albeerto-dev/Brewing_PLC/Images/Ricette_implementate.png

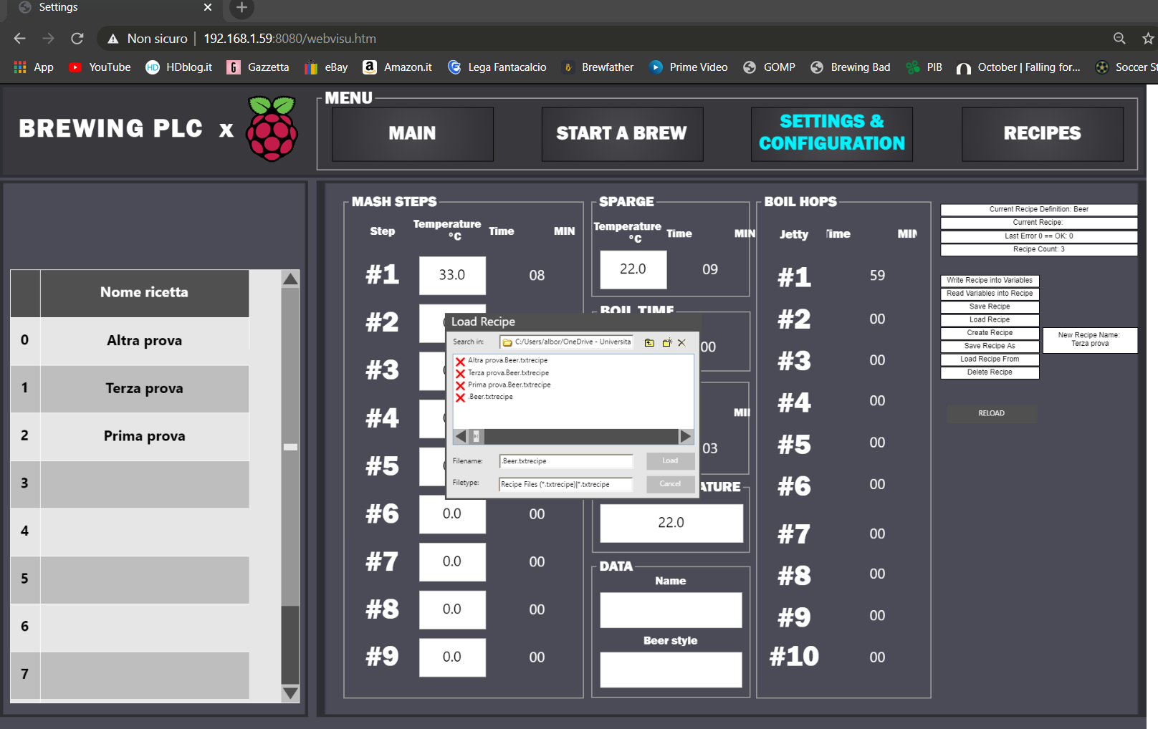
Images/Ricette_implementate.png
