albeerto-dev/Brewing_PLC/Images/WhatsApp Image 2020-11-09 at 20.25.59.jpeg

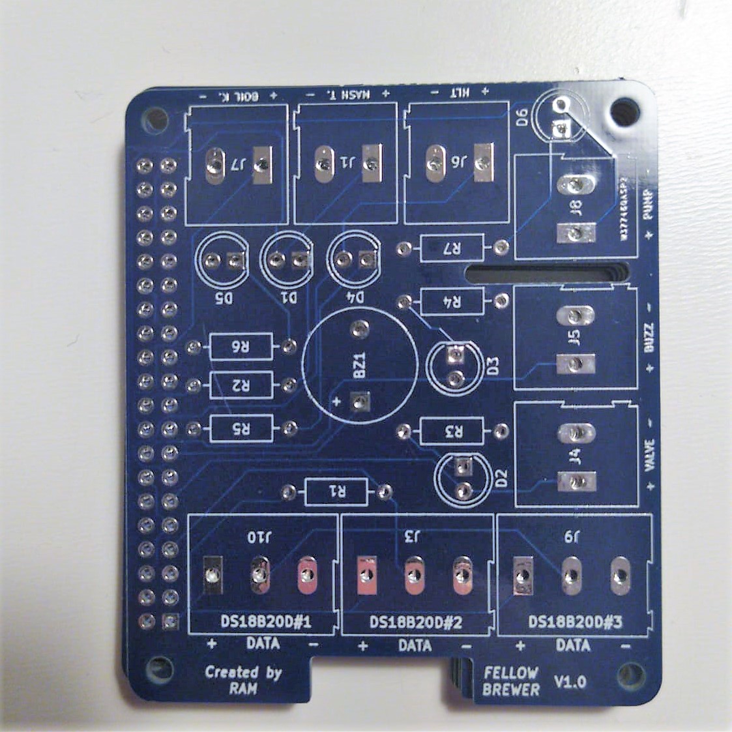
Images/WhatsApp Image 2020-11-09 at 20.25.59.jpeg
