albeerto-dev/Brewing_PLC/Schemi e PCB/Prove di schemi/PCB_PROV.png

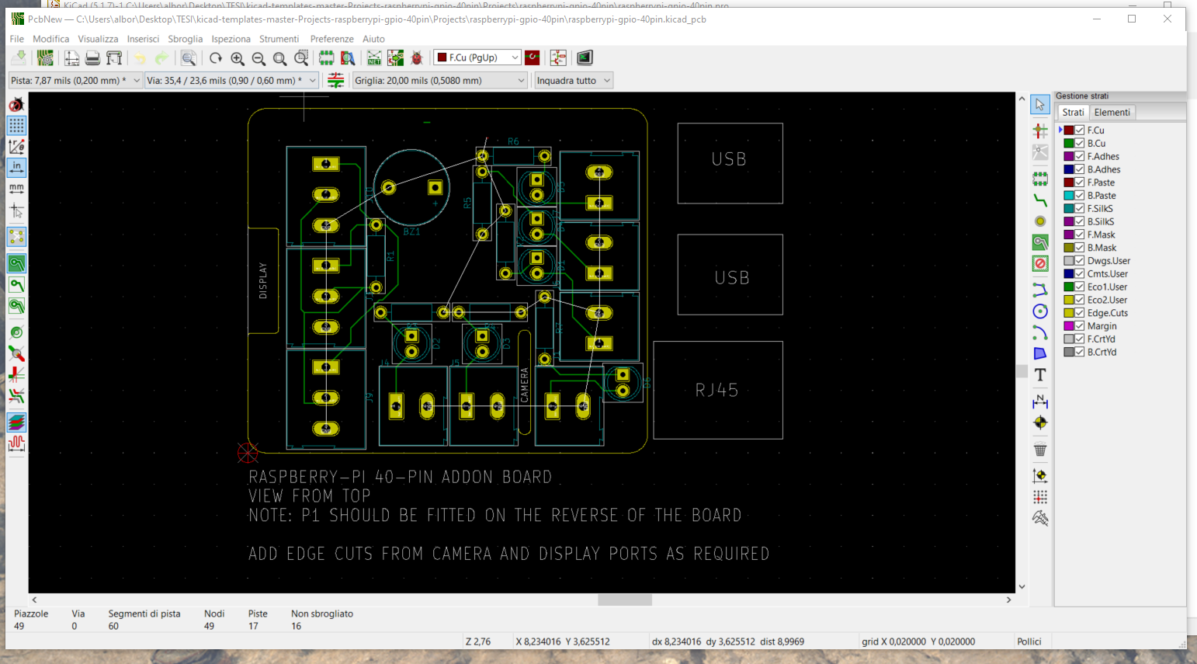
Schemi e PCB/Prove di schemi/PCB_PROV.png
